gamarrita/FMC-320U/Hardware/Modelo A/FMC-320U-A2/Project Outputs for FMC-320U-A2/Fabrication/Reports/DRC/FMC-320U-A2.html

Altium

# Design Rule Verification Report

Date: | | 1/12/2024
Time: | | 09:34:29
Elapsed Time: | | 00:00:01
Filename: | | C:\Users\Gamarra\AppData\Local\TempReleases\Snapshot\1\FMC-320U-A2.PcbDoc

Warnings: | | 0
Rule Violations: | | 0

## Summary

Warnings | Count
Total | 0

Rule Violations | Count
Clearance Constraint (Gap=0.2mm) (All),(All) | 0
Short-Circuit Constraint (Allowed=No) (All),(All) | 0
Un-Routed Net Constraint ( (All) ) | 0
Modified Polygon (Allow modified: No), (Allow shelved: No) | 0
Width Constraint (Min=0.2mm) (Max=5mm) (Preferred=0.2mm) (All) | 0
Power Plane Connect Rule(Relief Connect )(Expansion=0.508mm) (Conductor Width=0.254mm) (Air Gap=0.254mm) (Entries=4) (All) | 0
Hole Size Constraint (Min=0.3mm) (Max=10mm) (All) | 0
Hole To Hole Clearance (Gap=0.254mm) (All),(All) | 0
Minimum Solder Mask Sliver (Gap=0.2mm) (All),(All) | 0
Silk To Solder Mask (Clearance=0.2mm) (IsPad),(All) | 0
Silk to Silk (Clearance=0.2mm) (All),(All) | 0
Net Antennae (Tolerance=0mm) (All) | 0
Board Clearance Constraint (Gap=0mm) (All) | 0
Height Constraint (Min=0mm) (Max=25.4mm) (Prefered=12.7mm) (All) | 0
Total | 0
