gamarrita/FMC-320U/Hardware/Modelo A/FMC-320U-A2/Project Outputs for FMC-320U-A2/Fabrication/Reports/FootprintComparison/FMC-320U-A2.html

Altium customize

# Footprint Comparison Report

Date: | | 1/12/2024
Time: | | 09:34:32
Elapsed Time: | | 00:00:00
Filename: | | C:\Users\Gamarra\AppData\Local\TempReleases\Snapshot\1\FMC-320U-A2.PcbDoc

## Contents

Contents

Components Status Summary

Matched Components List

## Components Status Summary

## Matched Components List

Designator | Footprint | Footprint reference | Footprint to reference Library
B1 | STS40BD1BR3 | STS40BD1BR3 | C:\Users\Gamarra\AppData\Local\TempReleases\Snapshot\1\Dependencies\STS40BD1BR3.PcbLib
BH1 | BATTERY_HOLDER_2XAA | BATTERY_HOLDER_2XAA | C:\Users\Gamarra\AppData\Local\TempReleases\Snapshot\1\Dependencies\Battery_Holders.PcbLib
C1 | CAP_SM0805_YAGEOCC2_N | CAP_SM0805_YAGEOCC2_N | C:\Users\Gamarra\AppData\Local\TempReleases\Snapshot\1\Dependencies\Yageo.PcbLib
C2 | CAP_SM0805_YAGEOCC2_N | CAP_SM0805_YAGEOCC2_N | C:\Users\Gamarra\AppData\Local\TempReleases\Snapshot\1\Dependencies\Yageo.PcbLib
C3 | CAP_SM0805_YAGEOCC2_N | CAP_SM0805_YAGEOCC2_N | C:\Users\Gamarra\AppData\Local\TempReleases\Snapshot\1\Dependencies\Yageo.PcbLib
C4 | CAP_SM0805_YAGEOCC2_N | CAP_SM0805_YAGEOCC2_N | C:\Users\Gamarra\AppData\Local\TempReleases\Snapshot\1\Dependencies\Yageo.PcbLib
C5 | CAP_SM0805_YAGEOCC2_N | CAP_SM0805_YAGEOCC2_N | C:\Users\Gamarra\AppData\Local\TempReleases\Snapshot\1\Dependencies\Yageo.PcbLib
C6 | CAP_SM0805_YAGEOCC2_N | CAP_SM0805_YAGEOCC2_N | C:\Users\Gamarra\AppData\Local\TempReleases\Snapshot\1\Dependencies\Yageo.PcbLib
C7 | CAP_SM0805_YAGEOCC2_N | CAP_SM0805_YAGEOCC2_N | C:\Users\Gamarra\AppData\Local\TempReleases\Snapshot\1\Dependencies\Yageo.PcbLib
C8 | CAP_SM0805_YAGEOCC2_N | CAP_SM0805_YAGEOCC2_N | C:\Users\Gamarra\AppData\Local\TempReleases\Snapshot\1\Dependencies\Yageo.PcbLib
C9 | CAP_SM0805_YAGEOCC2_N | CAP_SM0805_YAGEOCC2_N | C:\Users\Gamarra\AppData\Local\TempReleases\Snapshot\1\Dependencies\Yageo.PcbLib
C12 | CAP_SM0805_YAGEOCC2_N | CAP_SM0805_YAGEOCC2_N | C:\Users\Gamarra\AppData\Local\TempReleases\Snapshot\1\Dependencies\Yageo.PcbLib
C13 | CAP_SM0805_YAGEOCC2_N | CAP_SM0805_YAGEOCC2_N | C:\Users\Gamarra\AppData\Local\TempReleases\Snapshot\1\Dependencies\Yageo.PcbLib
C14 | CAP_SM0805_YAGEOCC2_N | CAP_SM0805_YAGEOCC2_N | C:\Users\Gamarra\AppData\Local\TempReleases\Snapshot\1\Dependencies\Yageo.PcbLib
C15 | CAP_SM0805_YAGEOCC2_N | CAP_SM0805_YAGEOCC2_N | C:\Users\Gamarra\AppData\Local\TempReleases\Snapshot\1\Dependencies\Yageo.PcbLib
C16 | CAP_SM0805_YAGEOCC2_N | CAP_SM0805_YAGEOCC2_N | C:\Users\Gamarra\AppData\Local\TempReleases\Snapshot\1\Dependencies\Yageo.PcbLib
C17 | CAP_SM0805_YAGEOCC2_N | CAP_SM0805_YAGEOCC2_N | C:\Users\Gamarra\AppData\Local\TempReleases\Snapshot\1\Dependencies\Yageo.PcbLib
C18 | CAP_SM0805_YAGEOCC2_N | CAP_SM0805_YAGEOCC2_N | C:\Users\Gamarra\AppData\Local\TempReleases\Snapshot\1\Dependencies\Yageo.PcbLib
C20 | CAP_SM0805_YAGEOCC2_N | CAP_SM0805_YAGEOCC2_N | C:\Users\Gamarra\AppData\Local\TempReleases\Snapshot\1\Dependencies\Yageo.PcbLib
C21 | CAP_SM0805_YAGEOCC2_N | CAP_SM0805_YAGEOCC2_N | C:\Users\Gamarra\AppData\Local\TempReleases\Snapshot\1\Dependencies\Yageo.PcbLib
CN1 | DW200R-11-08-43 | DW200R-11-08-43 | C:\Users\Gamarra\AppData\Local\TempReleases\Snapshot\1\Dependencies\header_female.PcbLib
CN2 | DW200R-11-08-43 | DW200R-11-08-43 | C:\Users\Gamarra\AppData\Local\TempReleases\Snapshot\1\Dependencies\header_female.PcbLib
CN6 | HEADER PIN 2X10 | HEADER PIN 2X10 | C:\Users\Gamarra\AppData\Local\TempReleases\Snapshot\1\Dependencies\header_pin.PcbLib
CN8 | HEADER PIN 2X5 MIRROR | HEADER PIN 2X5 MIRROR | C:\Users\Gamarra\AppData\Local\TempReleases\Snapshot\1\Dependencies\header_pin.PcbLib
D1 | BAV23S | BAV23S | C:\Users\Gamarra\AppData\Local\TempReleases\Snapshot\1\Dependencies\diode.PcbLib
D2 | BAV23S | BAV23S | C:\Users\Gamarra\AppData\Local\TempReleases\Snapshot\1\Dependencies\diode.PcbLib
D3 | BAV23S | BAV23S | C:\Users\Gamarra\AppData\Local\TempReleases\Snapshot\1\Dependencies\diode.PcbLib
D4 | BAV23S | BAV23S | C:\Users\Gamarra\AppData\Local\TempReleases\Snapshot\1\Dependencies\diode.PcbLib
D5 | BAV23S | BAV23S | C:\Users\Gamarra\AppData\Local\TempReleases\Snapshot\1\Dependencies\diode.PcbLib
D6 | BAV23S | BAV23S | C:\Users\Gamarra\AppData\Local\TempReleases\Snapshot\1\Dependencies\diode.PcbLib
D7 | SMBJ28CA-13-F | SMBJ28CA-13-F | C:\Users\Gamarra\AppData\Local\TempReleases\Snapshot\1\Dependencies\diode.PcbLib
F1 | 0ZCJ0005FF2E | 0ZCJ0005FF2E | C:\Users\Gamarra\AppData\Local\TempReleases\Snapshot\1\Dependencies\fuse.PcbLib
J1 | HEADER PIN 1X3 | HEADER PIN 1X3 | C:\Users\Gamarra\AppData\Local\TempReleases\Snapshot\1\Dependencies\header_pin.PcbLib
J2 | HEADER PIN 2X4 | HEADER PIN 2X4 | C:\Users\Gamarra\AppData\Local\TempReleases\Snapshot\1\Dependencies\header_pin.PcbLib
J3 | HEADER PIN 1X2 | HEADER PIN 1X2 | C:\Users\Gamarra\AppData\Local\TempReleases\Snapshot\1\Dependencies\header_pin.PcbLib
J4 | HEADER PIN 1X2 | HEADER PIN 1X2 | C:\Users\Gamarra\AppData\Local\TempReleases\Snapshot\1\Dependencies\header_pin.PcbLib
J5 | HEADER PIN 1X2 | HEADER PIN 1X2 | C:\Users\Gamarra\AppData\Local\TempReleases\Snapshot\1\Dependencies\header_pin.PcbLib
J6 | HEADER PIN 1X2 | HEADER PIN 1X2 | C:\Users\Gamarra\AppData\Local\TempReleases\Snapshot\1\Dependencies\header_pin.PcbLib
P1 | HEADER PLUG 2 | HEADER PLUG 2 | C:\Users\Gamarra\AppData\Local\TempReleases\Snapshot\1\Dependencies\plug.PcbLib
P2 | HEADER PLUG 2 | HEADER PLUG 2 | C:\Users\Gamarra\AppData\Local\TempReleases\Snapshot\1\Dependencies\plug.PcbLib
P3 | HEADER PLUG 3 | HEADER PLUG 3 | C:\Users\Gamarra\AppData\Local\TempReleases\Snapshot\1\Dependencies\plug.PcbLib
P4 | HEADER PLUG 3 | HEADER PLUG 3 | C:\Users\Gamarra\AppData\Local\TempReleases\Snapshot\1\Dependencies\plug.PcbLib
PTH1 | PTH_M3_M | PTH_M3_M | C:\Users\Gamarra\AppData\Local\TempReleases\Snapshot\1\Dependencies\montaje.PcbLib
PTH2 | PTH_M3_M | PTH_M3_M | C:\Users\Gamarra\AppData\Local\TempReleases\Snapshot\1\Dependencies\montaje.PcbLib
PTH3 | PTH_M3_M | PTH_M3_M | C:\Users\Gamarra\AppData\Local\TempReleases\Snapshot\1\Dependencies\montaje.PcbLib
PTH4 | PTH_M3_M | PTH_M3_M | C:\Users\Gamarra\AppData\Local\TempReleases\Snapshot\1\Dependencies\montaje.PcbLib
Q2 | DMG3402L-7 | DMG3402L-7 | C:\Users\Gamarra\AppData\Local\TempReleases\Snapshot\1\Dependencies\mosfet.PcbLib
Q3 | DMG3401LSN-7 | DMG3401LSN-7 | C:\Users\Gamarra\AppData\Local\TempReleases\Snapshot\1\Dependencies\mosfet.PcbLib
R1 | RES_SM0805_YAGEORC_N | RES_SM0805_YAGEORC_N | C:\Users\Gamarra\AppData\Local\TempReleases\Snapshot\1\Dependencies\Yageo.PcbLib
R3 | RES_SM0805_YAGEORC_N | RES_SM0805_YAGEORC_N | C:\Users\Gamarra\AppData\Local\TempReleases\Snapshot\1\Dependencies\Yageo.PcbLib
R4 | RES_SM0805_YAGEORC_N | RES_SM0805_YAGEORC_N | C:\Users\Gamarra\AppData\Local\TempReleases\Snapshot\1\Dependencies\Yageo.PcbLib
R5 | RES_SM0805_YAGEORC_N | RES_SM0805_YAGEORC_N | C:\Users\Gamarra\AppData\Local\TempReleases\Snapshot\1\Dependencies\Yageo.PcbLib
R6 | RES_SM0805_YAGEORC_N | RES_SM0805_YAGEORC_N | C:\Users\Gamarra\AppData\Local\TempReleases\Snapshot\1\Dependencies\Yageo.PcbLib
R7 | RES_SM0805_YAGEORC_N | RES_SM0805_YAGEORC_N | C:\Users\Gamarra\AppData\Local\TempReleases\Snapshot\1\Dependencies\Yageo.PcbLib
R8 | RES_SM0805_YAGEORC_N | RES_SM0805_YAGEORC_N | C:\Users\Gamarra\AppData\Local\TempReleases\Snapshot\1\Dependencies\Yageo.PcbLib
R9 | RES_SM0805_YAGEORC_N | RES_SM0805_YAGEORC_N | C:\Users\Gamarra\AppData\Local\TempReleases\Snapshot\1\Dependencies\Yageo.PcbLib
R10 | RES_SM0805_YAGEORC_N | RES_SM0805_YAGEORC_N | C:\Users\Gamarra\AppData\Local\TempReleases\Snapshot\1\Dependencies\Yageo.PcbLib
R11 | RES_SM0805_YAGEORC_N | RES_SM0805_YAGEORC_N | C:\Users\Gamarra\AppData\Local\TempReleases\Snapshot\1\Dependencies\Yageo.PcbLib
R12 | RES_SM0805_YAGEORC_N | RES_SM0805_YAGEORC_N | C:\Users\Gamarra\AppData\Local\TempReleases\Snapshot\1\Dependencies\Yageo.PcbLib
R13 | RES_SM0805_YAGEORC_N | RES_SM0805_YAGEORC_N | C:\Users\Gamarra\AppData\Local\TempReleases\Snapshot\1\Dependencies\Yageo.PcbLib
R14 | RES_SM0805_YAGEORC_N | RES_SM0805_YAGEORC_N | C:\Users\Gamarra\AppData\Local\TempReleases\Snapshot\1\Dependencies\Yageo.PcbLib
R15 | RES_SM0805_YAGEORC_N | RES_SM0805_YAGEORC_N | C:\Users\Gamarra\AppData\Local\TempReleases\Snapshot\1\Dependencies\Yageo.PcbLib
R26 | RES_SM0805_YAGEORC_N | RES_SM0805_YAGEORC_N | C:\Users\Gamarra\AppData\Local\TempReleases\Snapshot\1\Dependencies\Yageo.PcbLib
R27 | RES_SM0805_YAGEORC_N | RES_SM0805_YAGEORC_N | C:\Users\Gamarra\AppData\Local\TempReleases\Snapshot\1\Dependencies\Yageo.PcbLib
R28 | RES_SM0805_YAGEORC_N | RES_SM0805_YAGEORC_N | C:\Users\Gamarra\AppData\Local\TempReleases\Snapshot\1\Dependencies\Yageo.PcbLib
R29 | RES_SM0805_YAGEORC_N | RES_SM0805_YAGEORC_N | C:\Users\Gamarra\AppData\Local\TempReleases\Snapshot\1\Dependencies\Yageo.PcbLib
R30 | RES_SM0805_YAGEORC_N | RES_SM0805_YAGEORC_N | C:\Users\Gamarra\AppData\Local\TempReleases\Snapshot\1\Dependencies\Yageo.PcbLib
R31 | RES_SM0805_YAGEORC_N | RES_SM0805_YAGEORC_N | C:\Users\Gamarra\AppData\Local\TempReleases\Snapshot\1\Dependencies\Yageo.PcbLib
U1 | MCP6541-E/SN | MCP6541-E/SN | C:\Users\Gamarra\AppData\Local\TempReleases\Snapshot\1\Dependencies\OP_Amps.PcbLib

Back to top
