gamarrita/FMC-320U/docs/analisis/costs/expenses/Invoice primer prototito/Proforma  Invoice - ACTUALIZADA.pdf

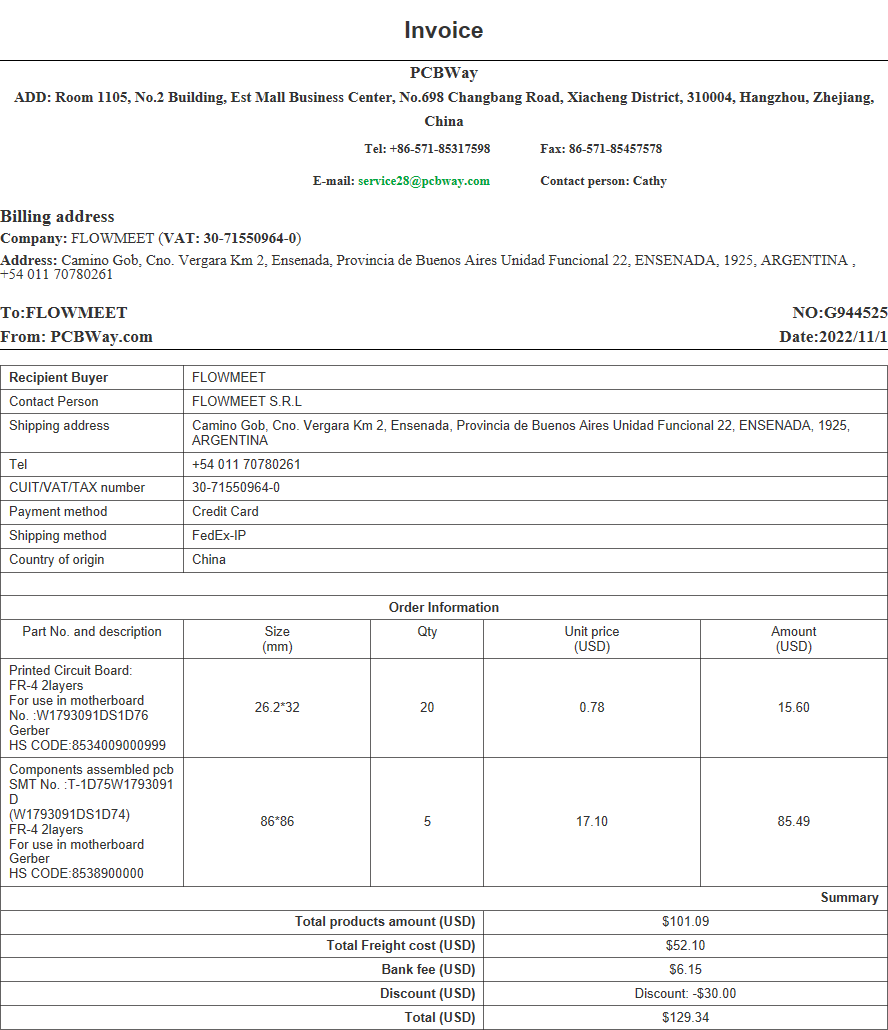
[picture p45: page 1]
