gamarrita/FMC-320U/docs/analisis/costs/expenses/Invoice primer prototito/Proforma Invoice - 20221101220300.pdf

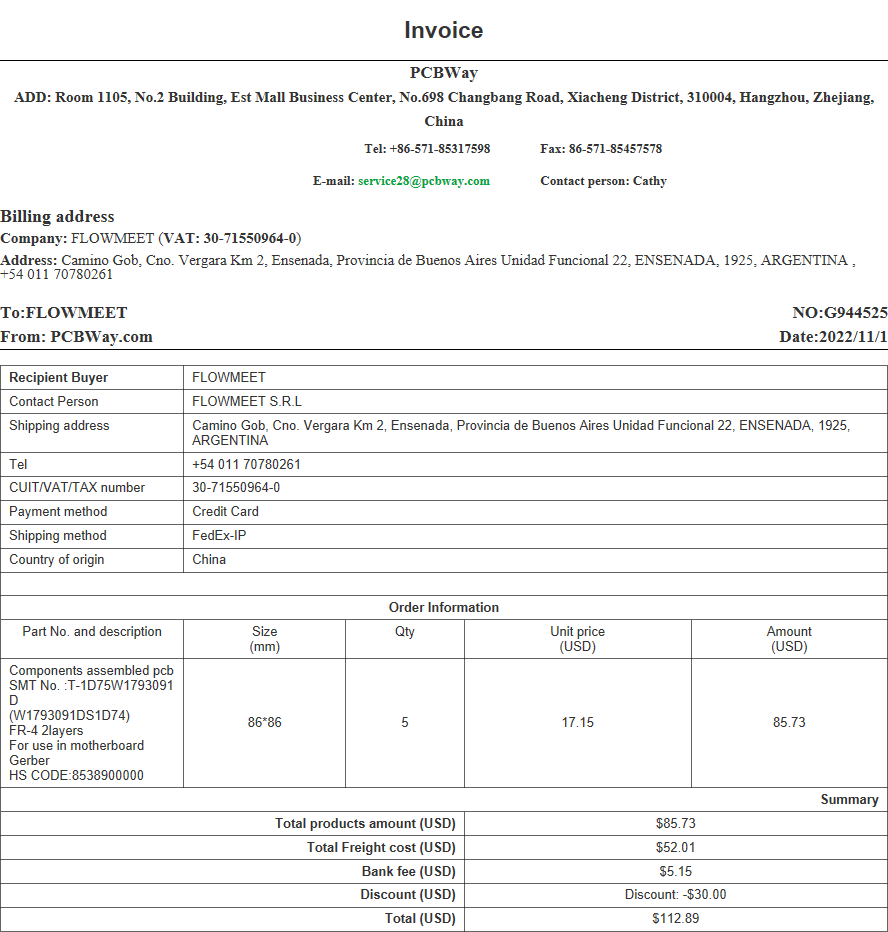
[picture p46: page 1]
