gamarrita/FMC-320U/Firmware/app/Docs/FMC-320U-A2 V1R2R1.pdf

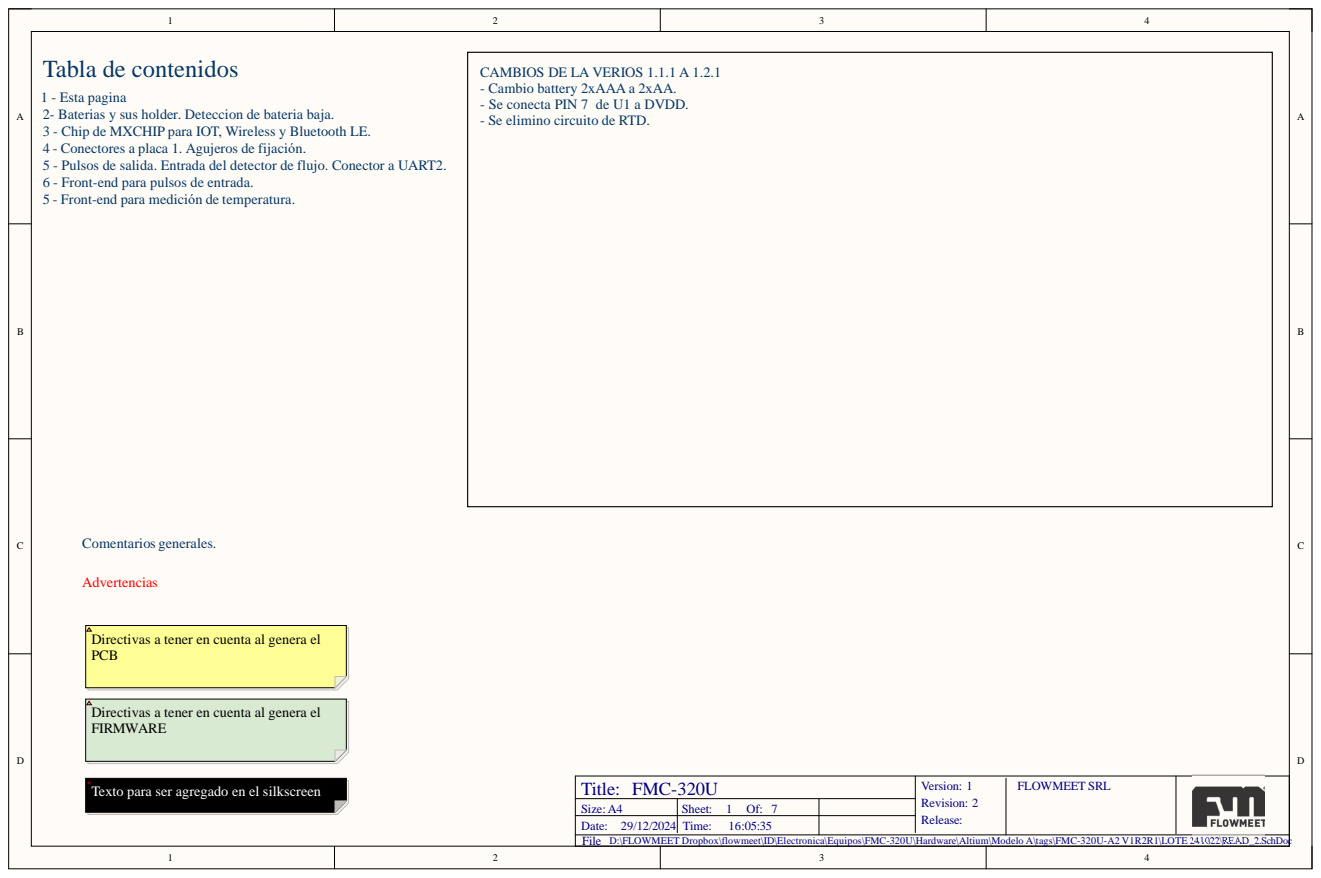
[picture p82: page 1]

CAMBIOS DE LA VERIOS 1.1.1 A 1.2.1
- Cambio battery 2xAAA a 2xAA.
- Se conecta PIN 7 de U1 a DVDD.
- Se elimino circuito de RTD.

1 - Esta pagina
2- Baterias y sus holder. Deteccion de bateria baja.
3 - Chip de MXCHIP para IOT, Wireless y Bluetooth LE.
4 - Conectores a placa 1. Agujeros de fijación.
5 - Pulsos de salida. Entrada del detector de flujo. Conector a UART2.
6 - Front-end para pulsos de entrada.
5 - Front-end para medición de temperatura.

Directivas a tener en cuenta al genera el
PCB

FIRMWARE

Title: FMC-320U | Version: 1 Revision: 2 Release: | FLOWMEET SRL

Texto para ser agregado en el silkscreen

Size: A4 | Sheet: 1 Of: 7
Date: 29/12/2024 | Time: 16:05:35

File
D:\FLOWMEET Dropbox\flowmeet\ID\Electronica\Equipos\FMC-320U\Hardware\Altium\Modelo A\tags\FMC-320U-A2 V1R2R1\LOTE 241022\READ_2.SchDoc

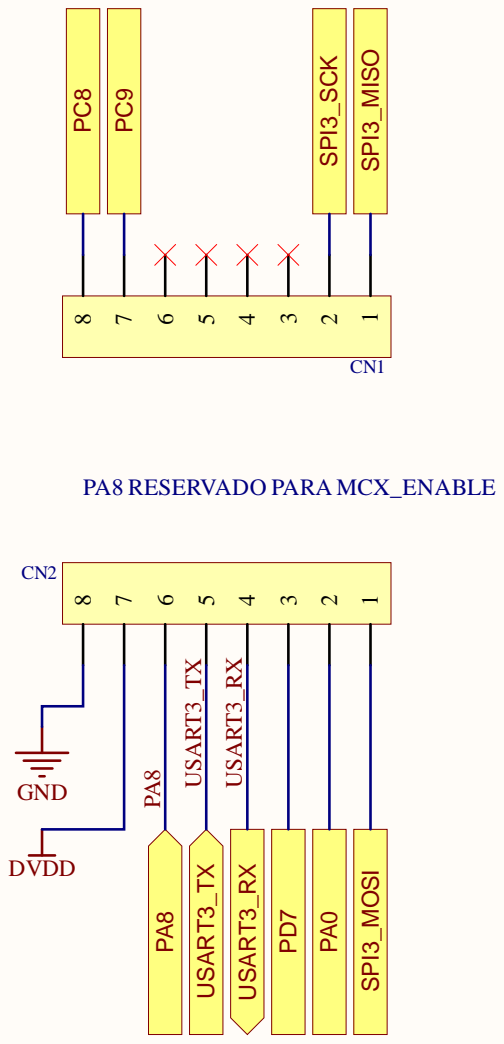
[picture p83: page 2]

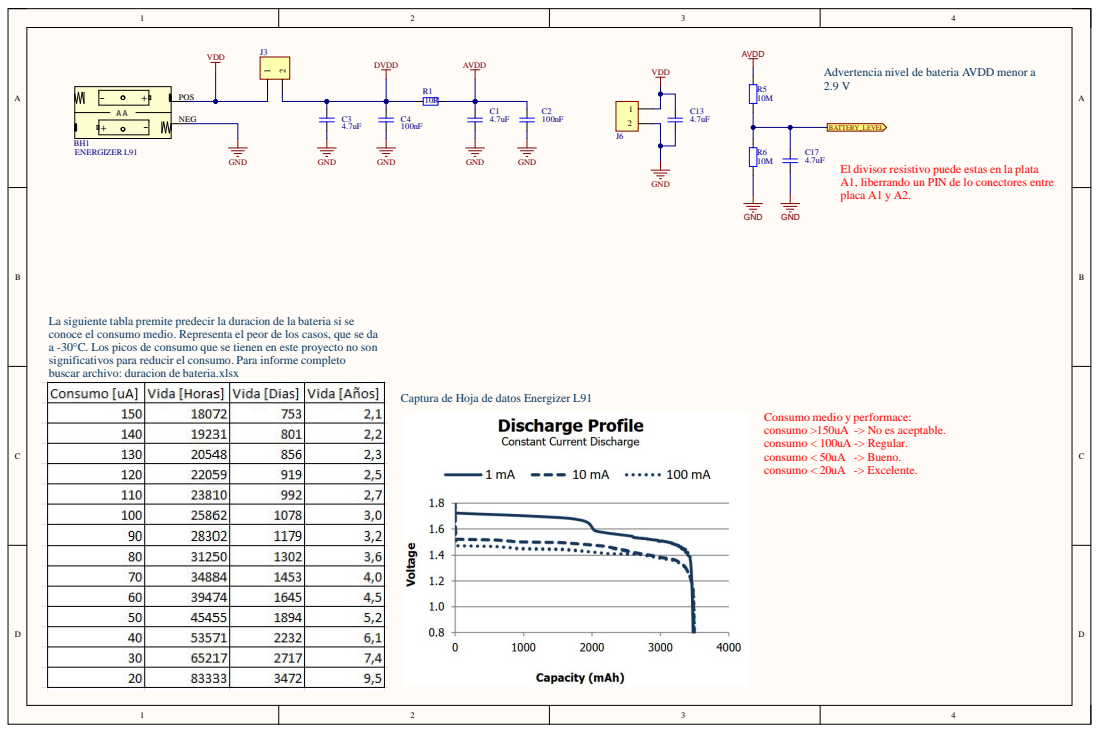
[picture p84: page 3]

Advertencia nivel de bateria

ivo puede estas en

La siguiente
conoce el consumo
significat
buscar archivo: duracion de bateria.xlsx

tabla prem
medio. Representa el peor de

la bateria si se
los casos, que se da

°C. Los picos de consumo que se
ivos para reducir el consumo. Para

ienen en este proyecto no son

Hoja de datos Energizer L91

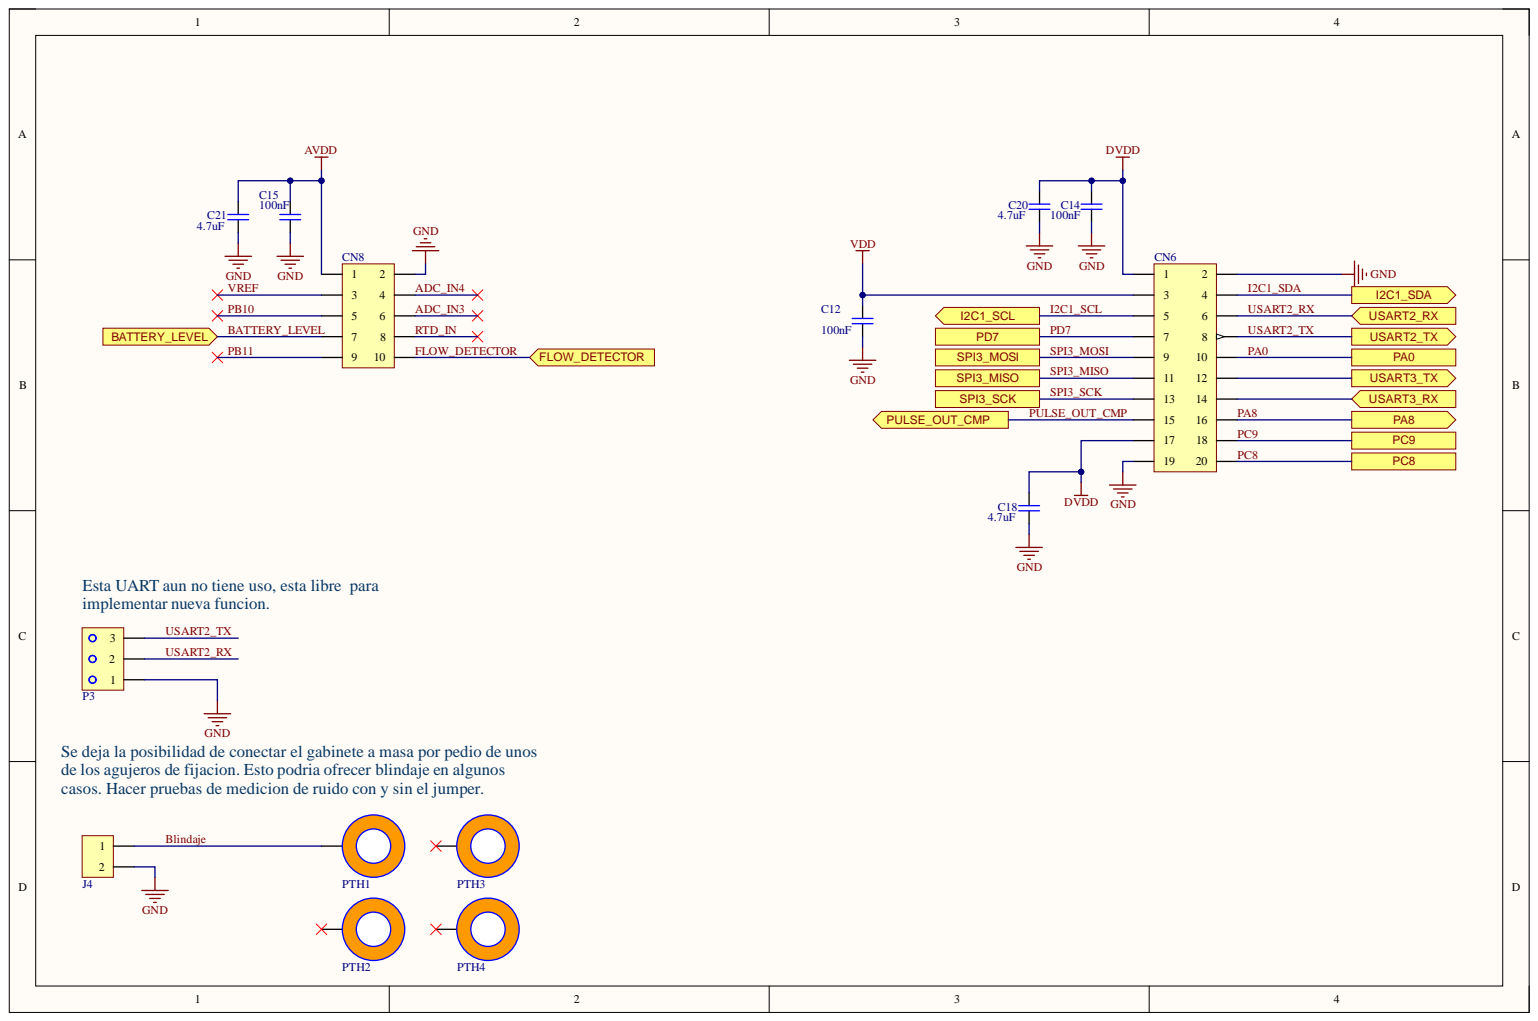
[picture p85: page 4]

Esta UART aun no tiene uso, esta libre para
implementar nueva funcion.

Se deja la posibilidad de conectar el gabinete a masa por pedio de unos
de los agujeros de fijacion. Esto podria ofrecer blindaje en algunos
casos. Hacer pruebas de medicion de ruido con y sin el jumper.

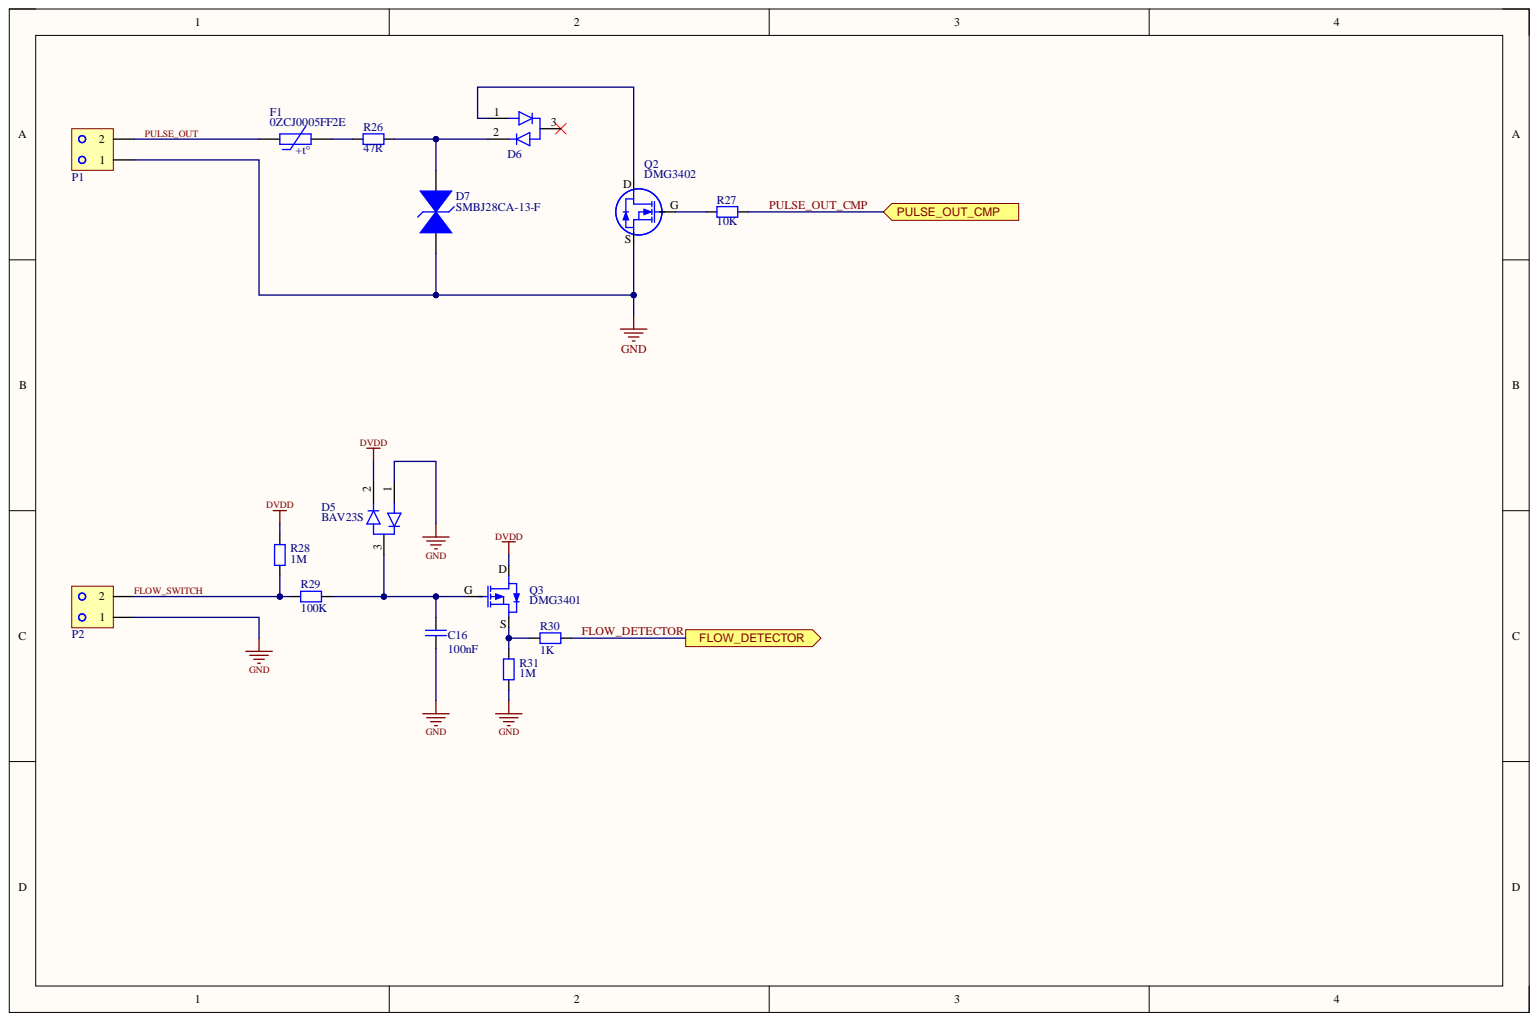
[picture p86: page 5]

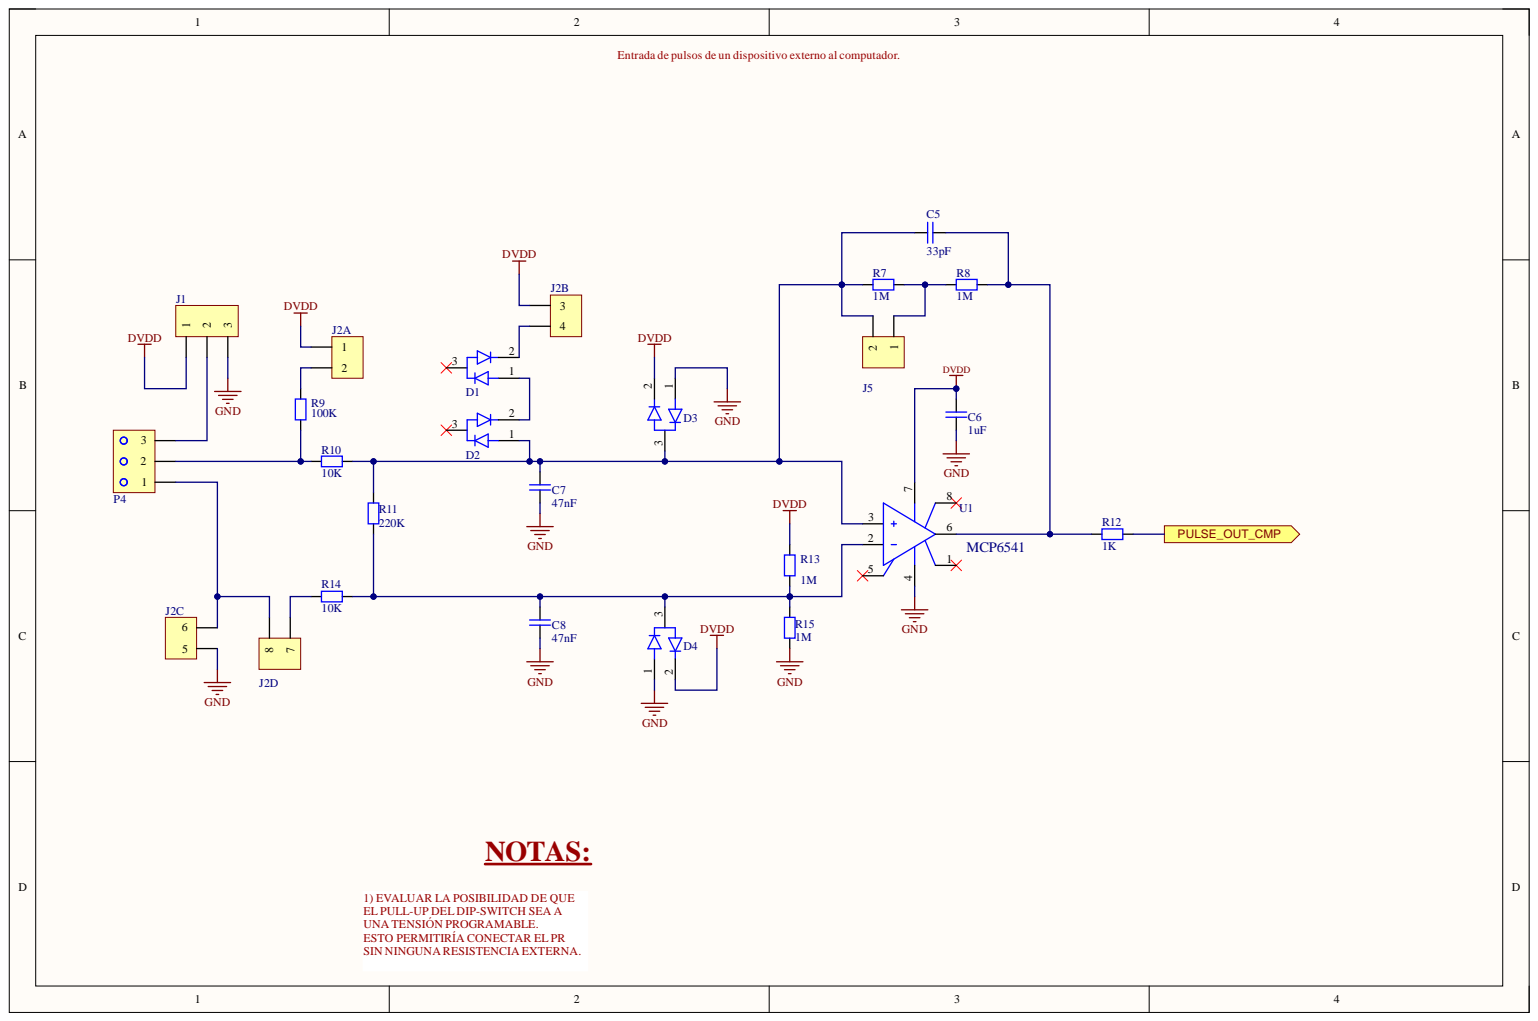
[picture p87: page 6]

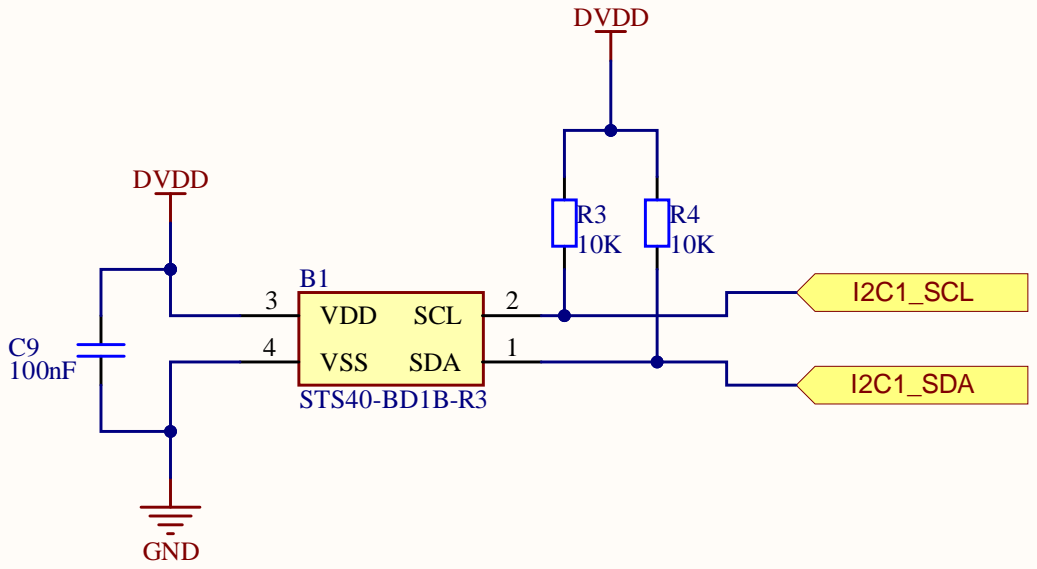
[picture p88: page 7]

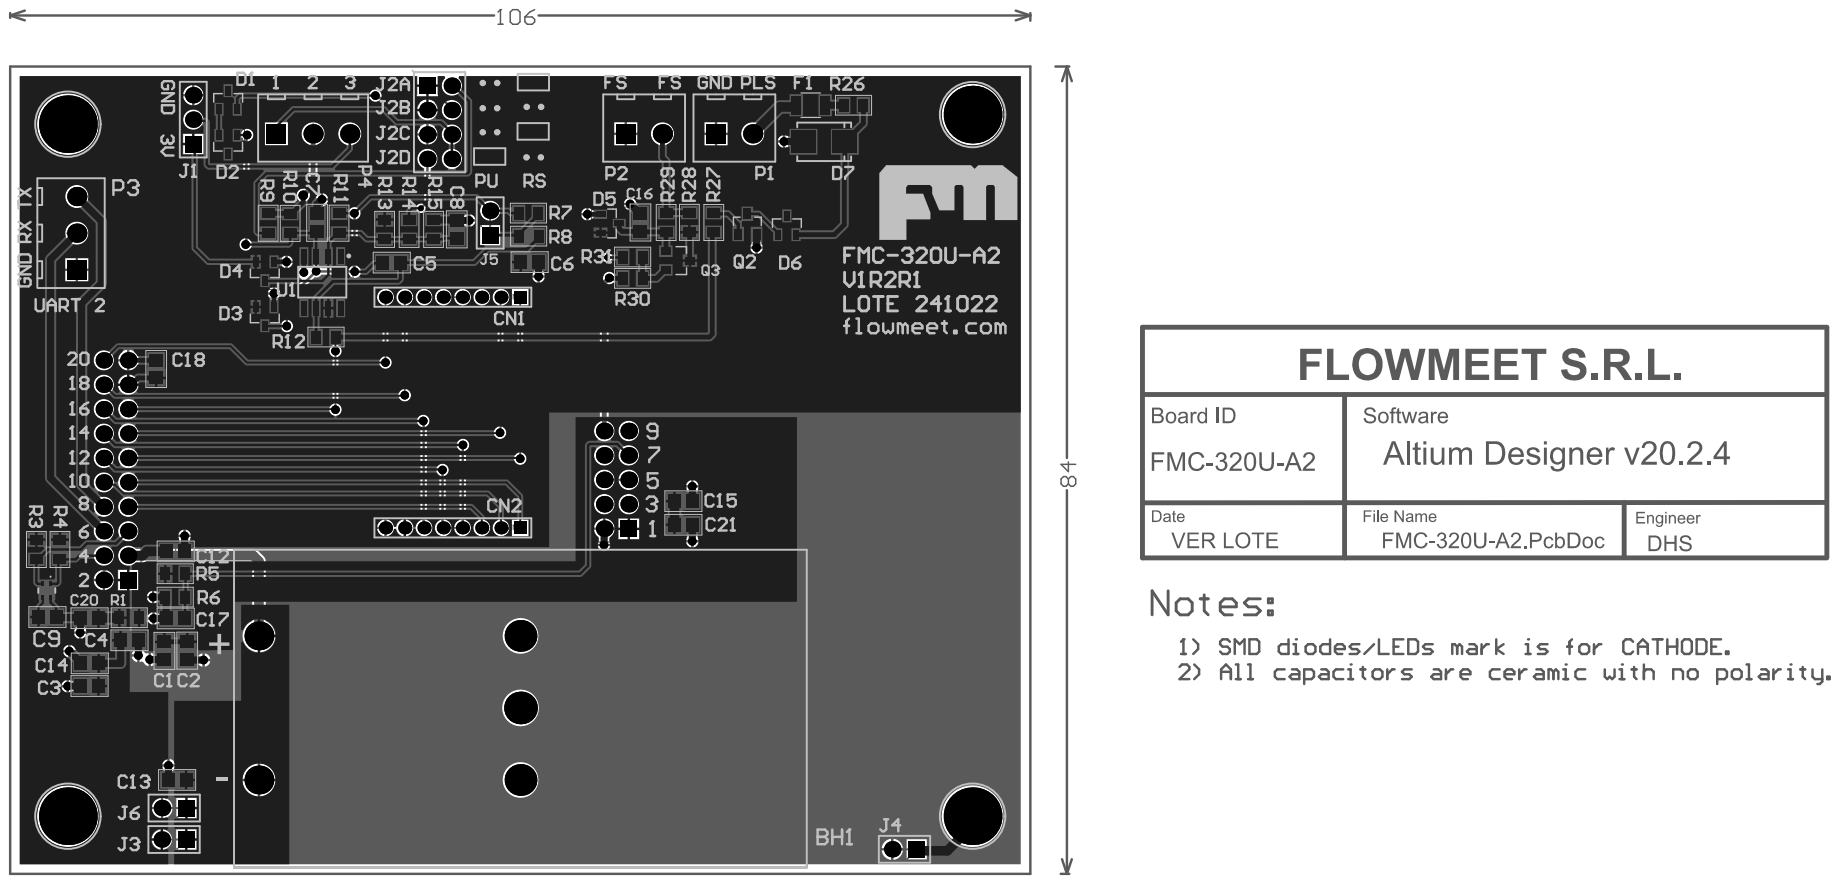
[picture p89: page 8]
