gamarrita/FMC-320U/Hardware/Modelo A/FMC-320U-A2/Project Outputs for FMC-320U-A2/Assembly/AssemblyDrawing.pdf

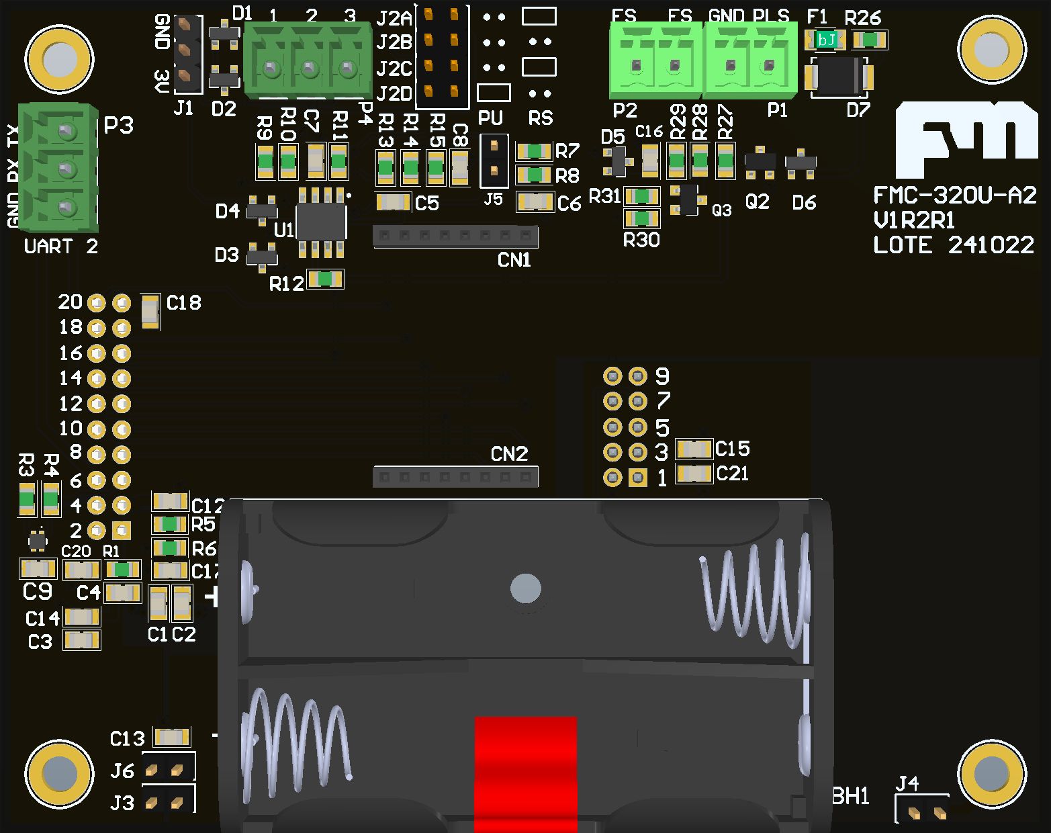
[picture p91: page 1]

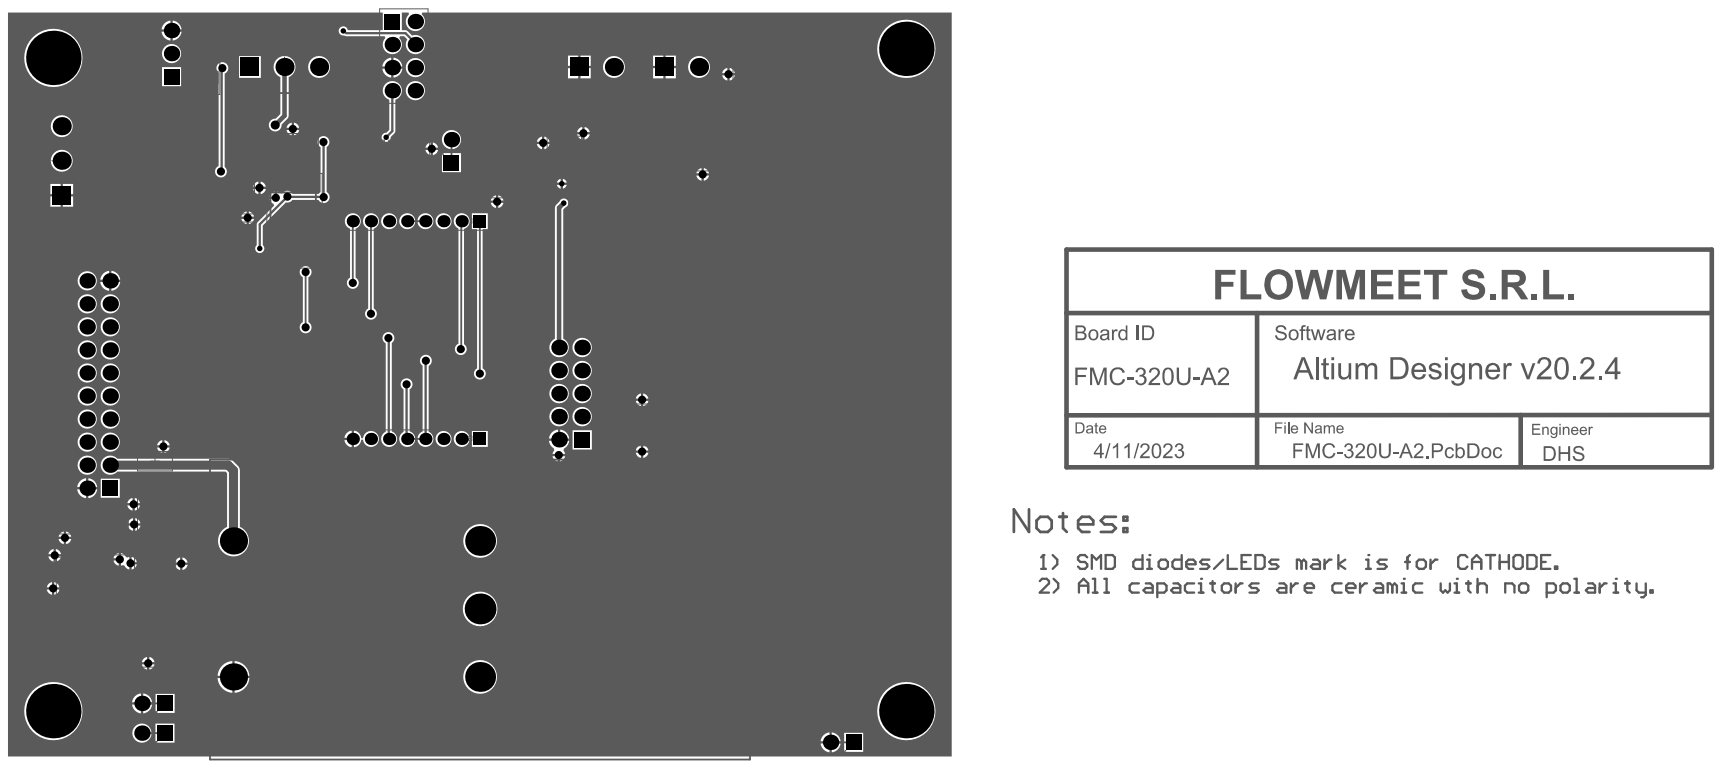
[picture p92: page 2]

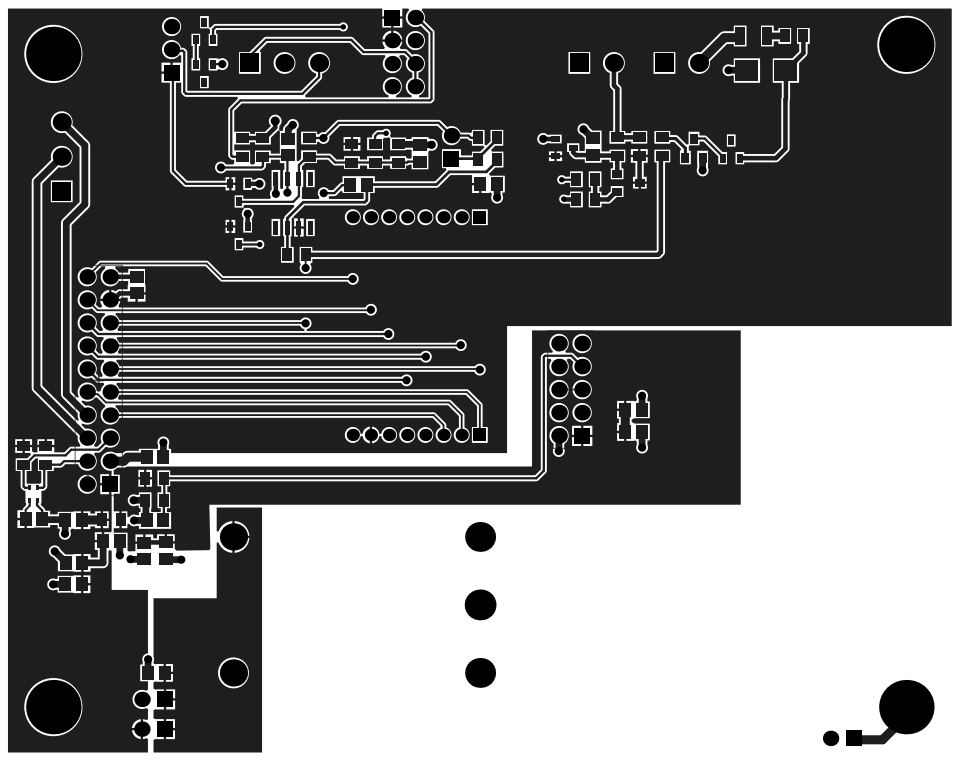
[picture p93: page 3]
