gamarrita/FMC-320U/Hardware/Modelo A/FMC-320U-A2/Project Outputs for FMC-320U-A2/Fabrication/Fabrication.pdf

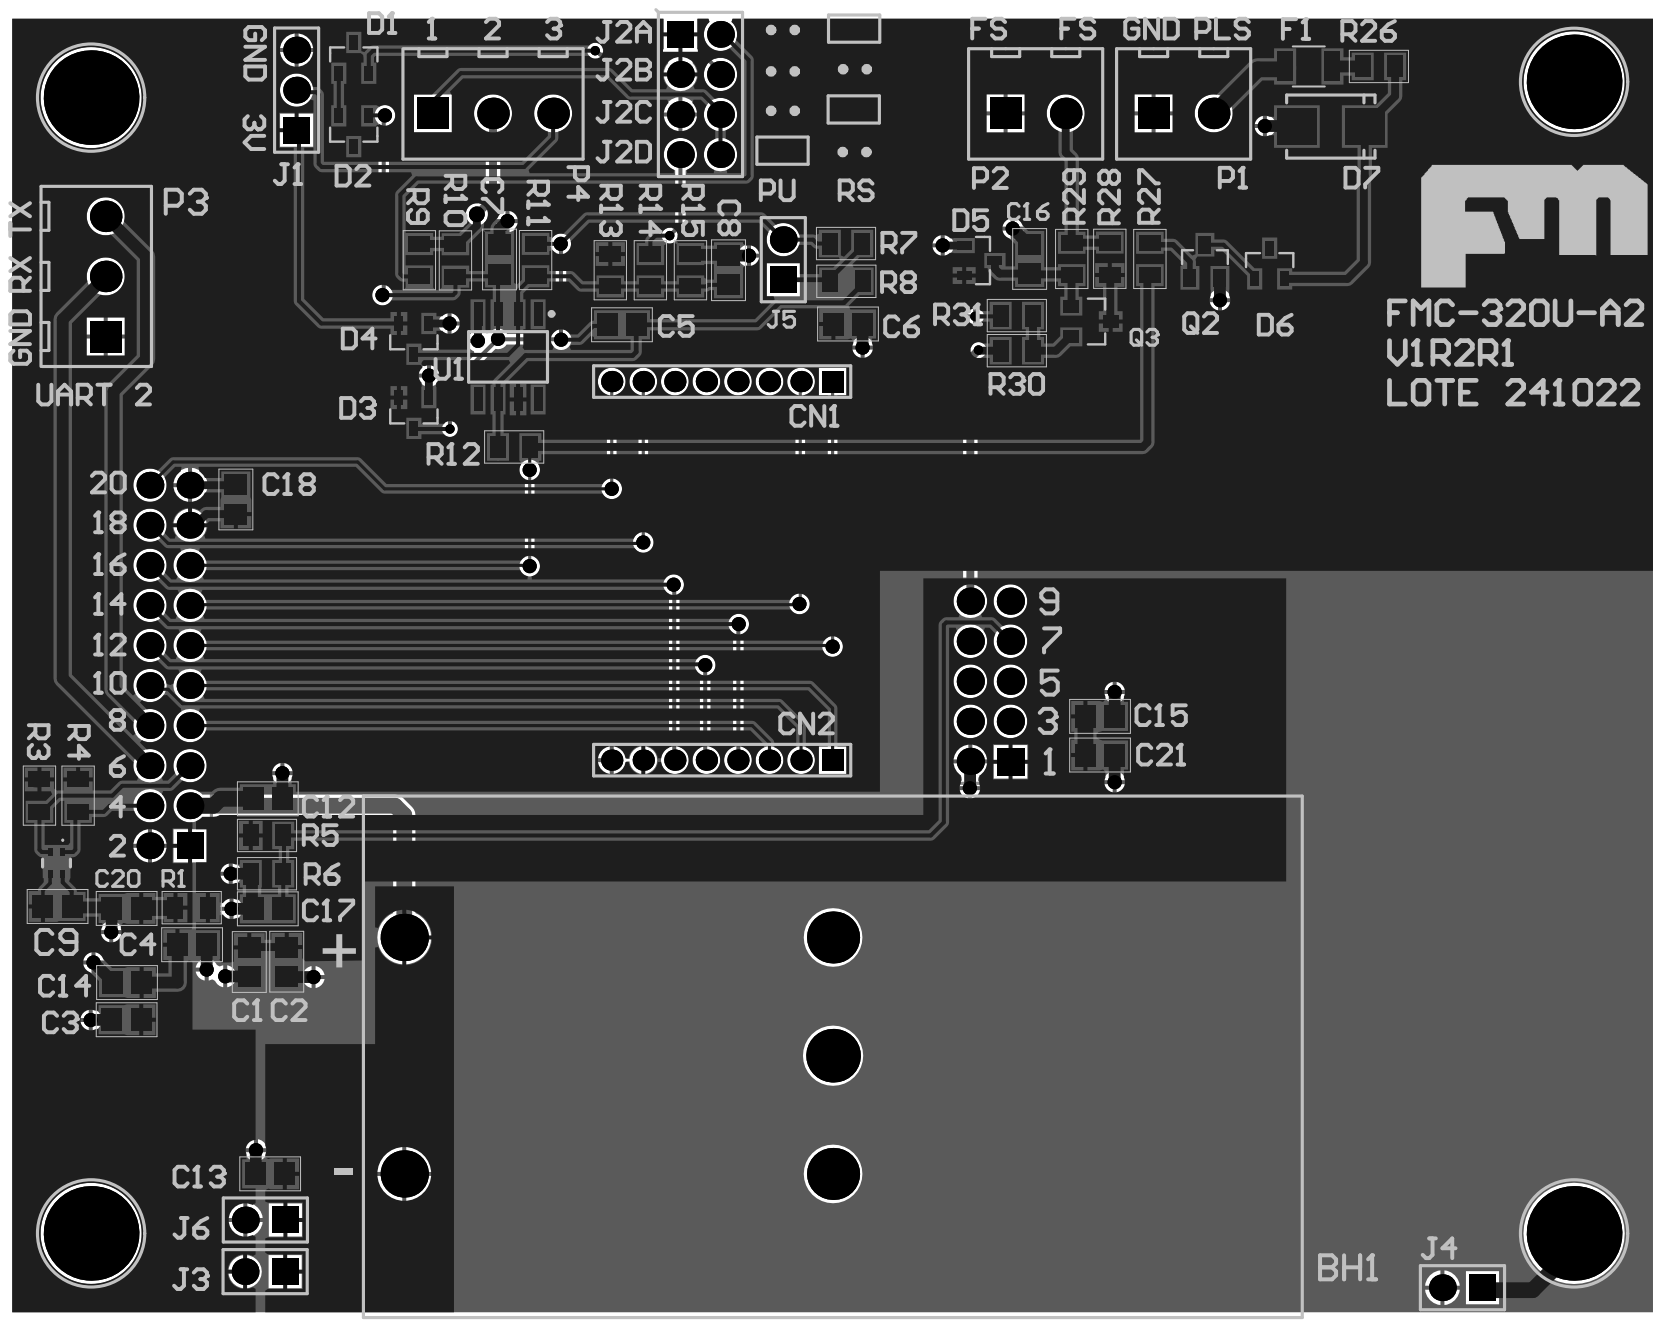
[picture p94: page 1]
