gamarrita/FMC-320U/Firmware/app/103_lptim3_dma/FLOWMEET/fm_main.h

/*
 *
 *
 */

#ifndef FM_MAIN_H_
#define FM_MAIN_H_

// includes

// Typedef y enum.

// Macros, defines, microcontroller pins (dhs).

// Varibles extern

// Defines.

// Function prototypes
void FM_MAIN_Main();

#endif  // FM_MAIN_H

/*** end of file ***/
